robot-stefan/telescope/images/camping2.jpg

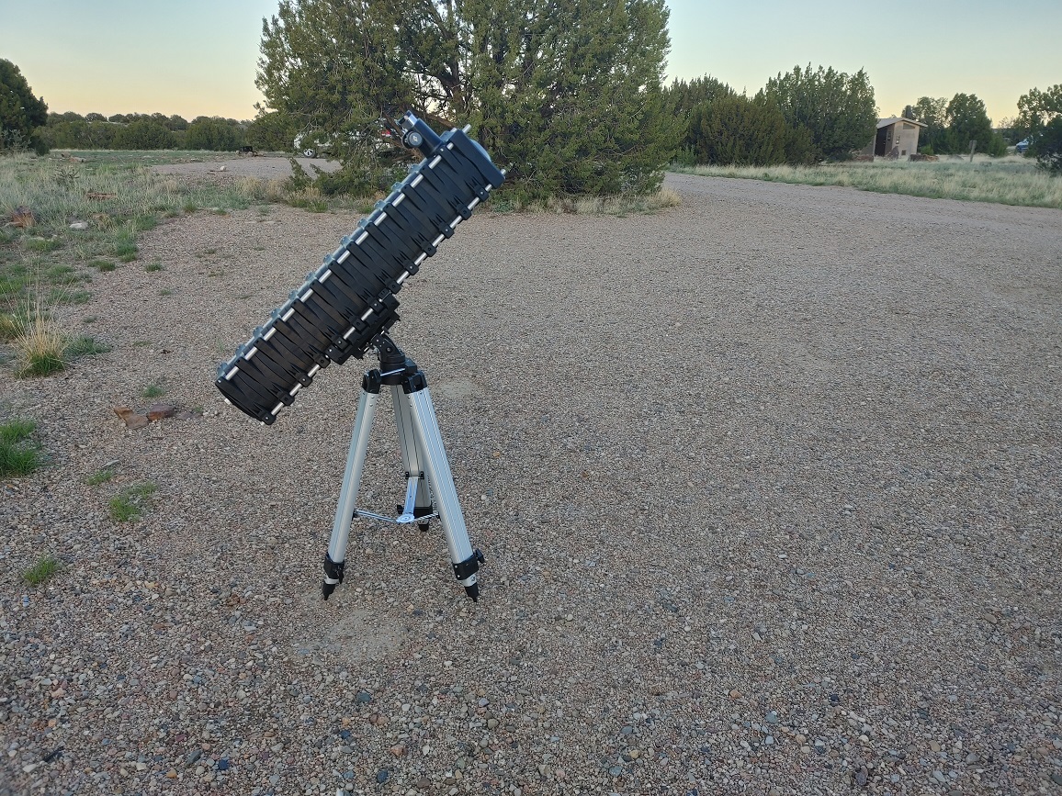
images/camping2.jpg
