robot-stefan/telescope/images/physical_mockup.jpg

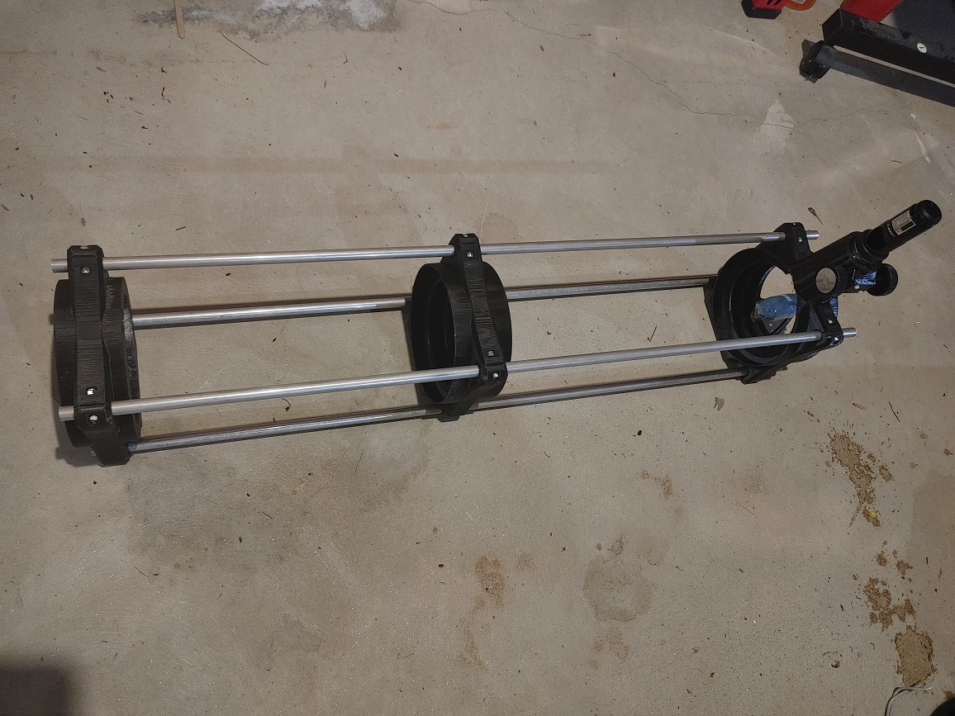
images/physical_mockup.jpg
