robot-stefan/telescope/images/ray-without-cad.png

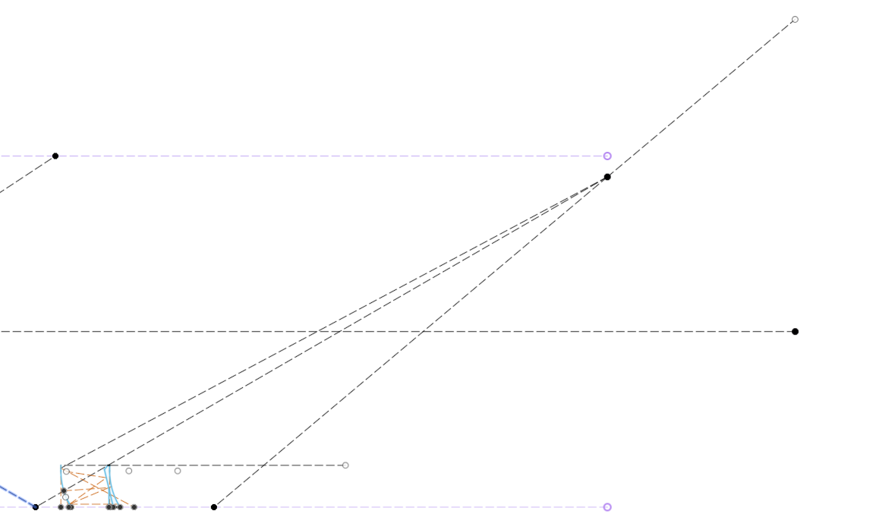
images/ray-without-cad.png
