robot-stefan/telescope/images/Screenshot_2023-09-21-154836.png

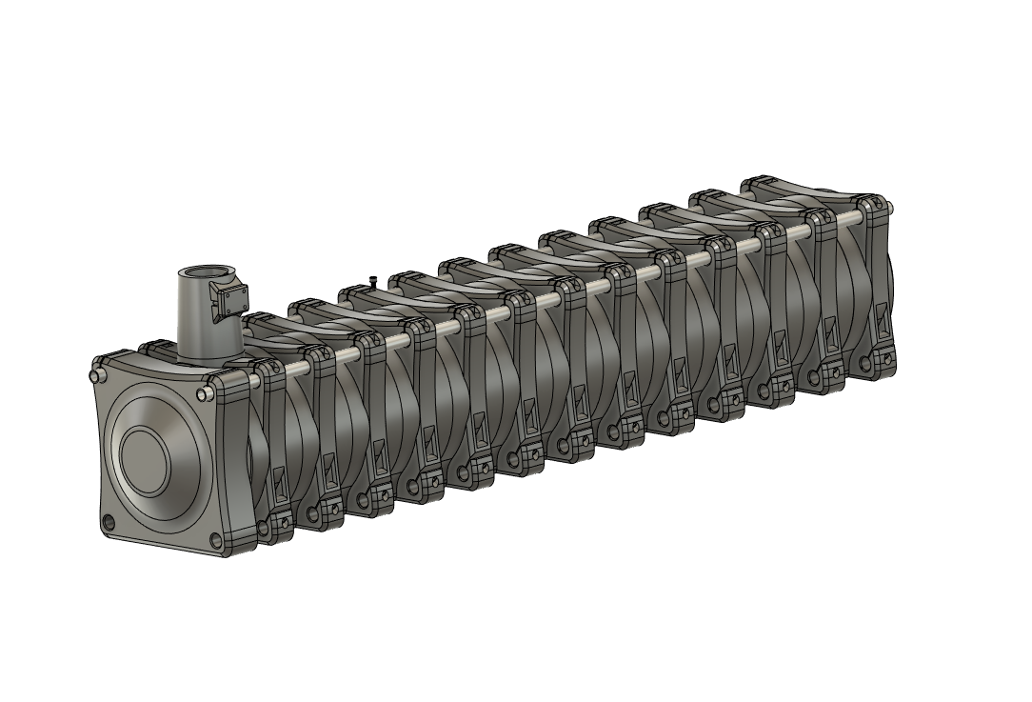
images/Screenshot_2023-09-21-154836.png
