robot-stefan/telescope/images/Screenshot_2023-09-21-155059.png

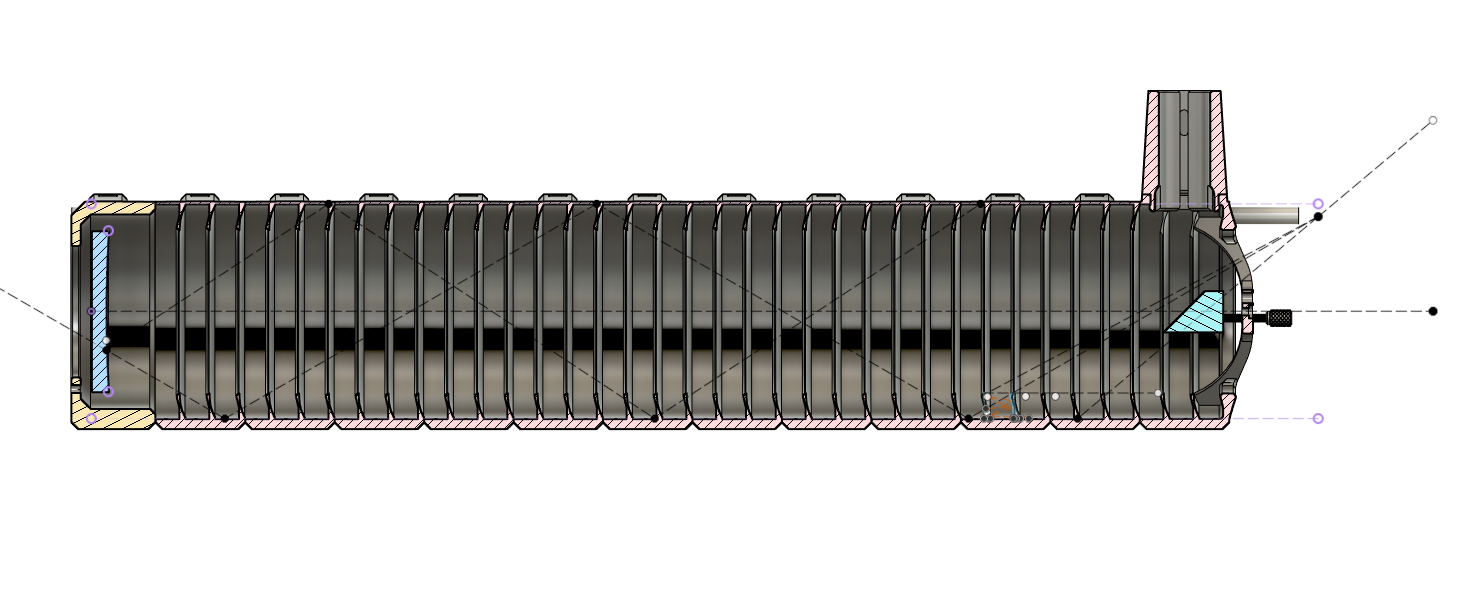
images/Screenshot_2023-09-21-155059.png
