robot-stefan/telescope/images/view_showingPrimaryAdjust.jpg

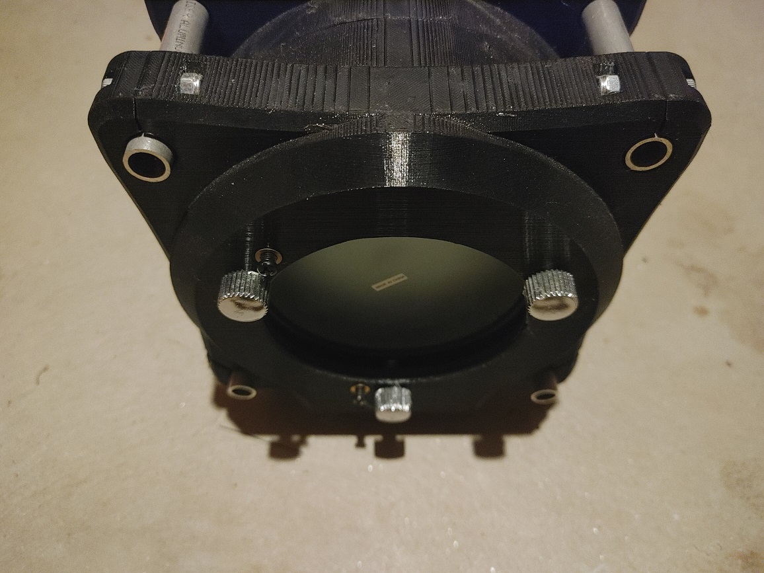
images/view_showingPrimaryAdjust.jpg
