robot-stefan/telescope/images/view_showingSecondaryAdjust.jpg

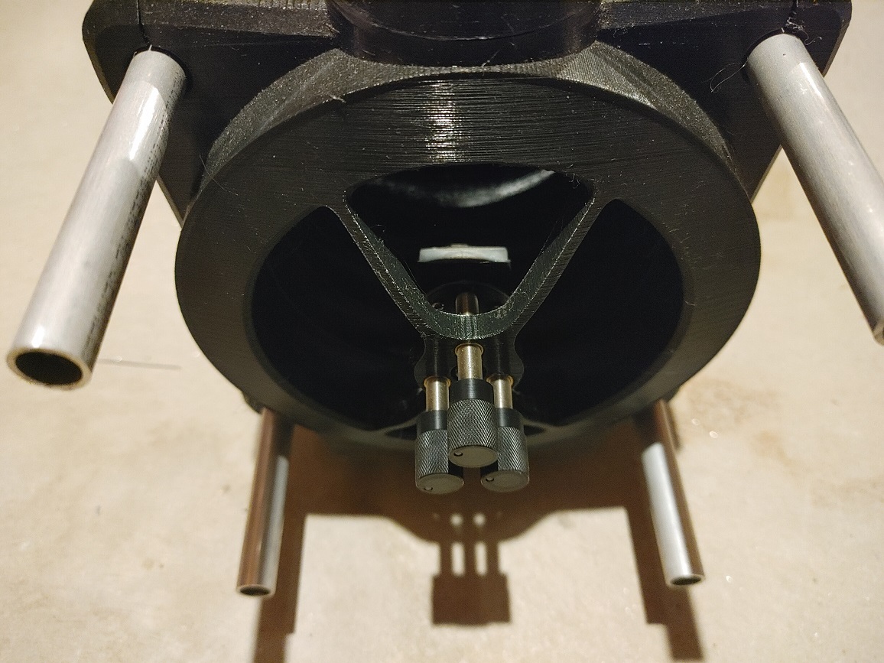
images/view_showingSecondaryAdjust.jpg
