robot-stefan/telescope/images/view_showingTopEyePiece.jpg

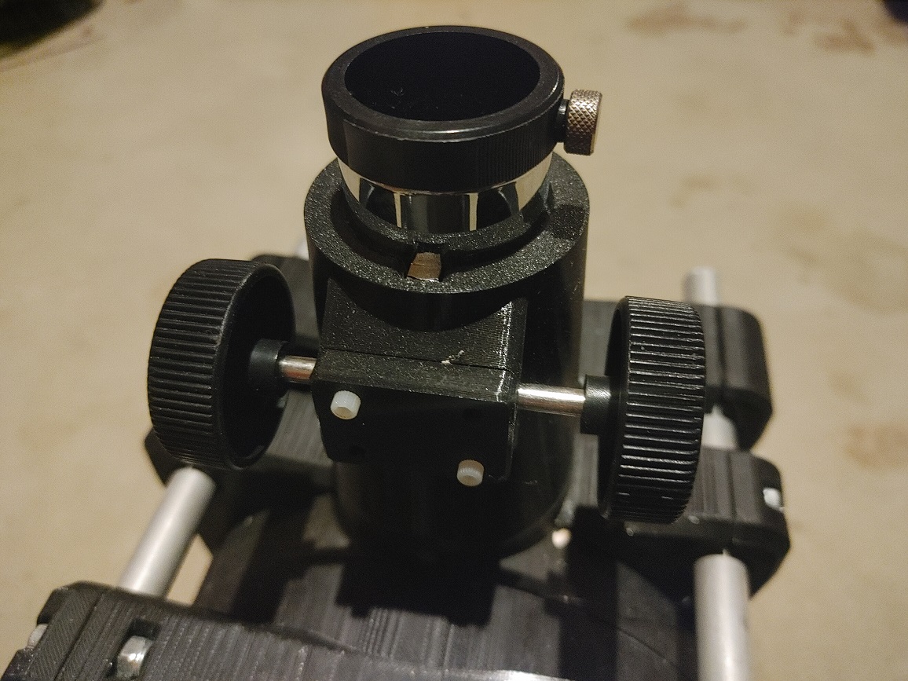
images/view_showingTopEyePiece.jpg
