robot-stefan/telescope/images/assembled.jpg

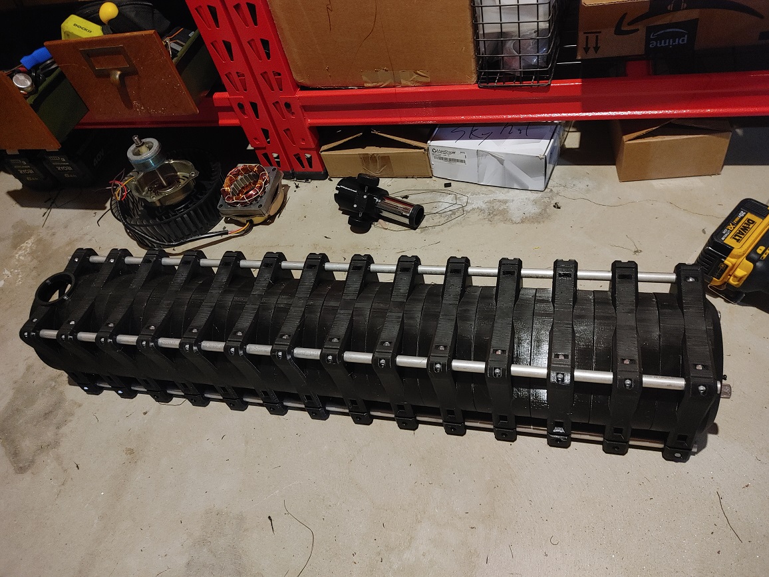
images/assembled.jpg
