robot-stefan/telescope/images/print_fail.jpg

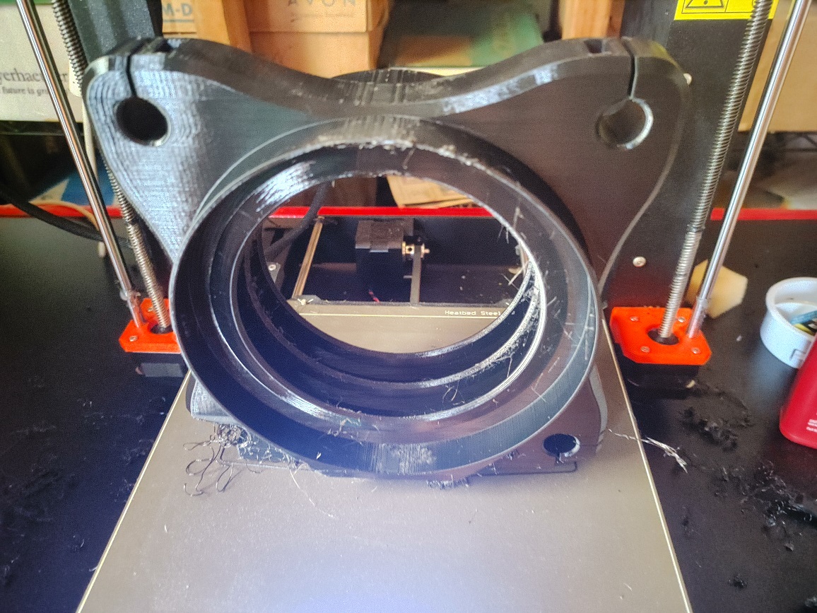
images/print_fail.jpg
