robot-stefan/telescope/images/print_in_progress.jpg

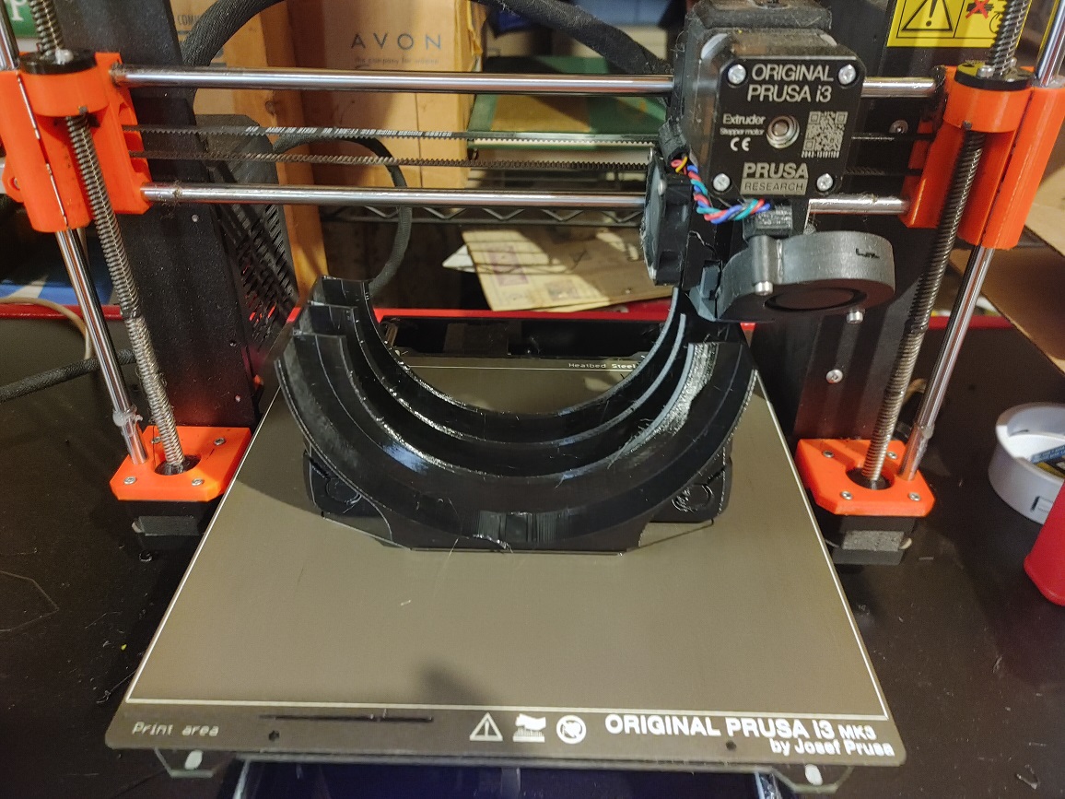
images/print_in_progress.jpg
